friedpies/phaedr-midi-controller/.planning/phases/01-mcu-protocol-foundation/01-04-PLAN.md

---
phase: 01-mcu-protocol-foundation
plan: "04"
type: execute
wave: 1
depends_on: []
files_modified:
  - src/mcuProtocol.h
  - src/mcuProtocol.cpp
autonomous: true
requirements:
  - MCU-01
  - MCU-02

must_haves:
  truths:
    - "Device sends correct Host Connection Query (Step 2) when Logic Pro's Device Query arrives"
    - "Challenge-response validation correctly computes expected bytes from the 4 challenge bytes"
    - "Device sends Confirmation (Step 4) when Logic's reply matches the expected response"
    - "If Logic does not respond, device retries unsolicited Host Connection Query every 5 seconds"
    - "Handshake complete flag is set and accessible after Step 4 confirmation"
  artifacts:
    - path: "src/mcuProtocol.h"
      provides: "MCUProtocol class — SysEx handshake state machine"
      contains: "class MCUProtocol"
    - path: "src/mcuProtocol.cpp"
      provides: "Handshake implementation with challenge-response algorithm"
      contains: "validateChallengeResponse"
  key_links:
    - from: "src/mcuProtocol.cpp"
      to: "usbMIDI.sendSysEx"
      via: "Host Connection Query and Confirmation messages"
      pattern: "sendSysEx"
    - from: "src/mcuProtocol.cpp"
      to: "challenge-response"
      via: "validateChallengeResponse computing expected[0..3]"
      pattern: "expected\\[0\\].*0x7F"
---

<objective>
Create the MCUProtocol class that handles the 4-step Mackie Control Universal SysEx handshake with Logic Pro. This is what causes Logic to recognize the controller as a Mackie Control surface and begin sending bidirectional MIDI feedback.

Purpose: Without a successful handshake, Logic Pro sends no LED feedback and does not route button/fader input to the correct tracks. This is the single gating dependency for the entire phase.
Output: src/mcuProtocol.h and src/mcuProtocol.cpp
</objective>

<execution_context>
@/Users/kenmarut/.claude/get-shit-done/workflows/execute-plan.md
@/Users/kenmarut/.claude/get-shit-done/templates/summary.md
</execution_context>

<context>
@.planning/PROJECT.md
@.planning/ROADMAP.md
@src/pinDefines.h
</context>

<tasks>

<task type="auto">
  <name>Task 1: Create MCUProtocol class — SysEx handshake state machine</name>
  <files>src/mcuProtocol.h, src/mcuProtocol.cpp</files>
  <action>
Create `src/mcuProtocol.h` and `src/mcuProtocol.cpp` implementing the 4-step MCU SysEx handshake.

**Handshake flow (Logic sends first):**
```
Step 1: Logic → Device:  F0 00 00 66 14 00 F7  (Device Query)
Step 2: Device → Logic:  F0 00 00 66 14 01 [serial 7 bytes] [challenge 4 bytes] F7
Step 3: Logic → Device:  F0 00 00 66 14 02 [serial 7 bytes] [response 4 bytes] F7
Step 4: Device → Logic:  F0 00 00 66 14 03 [serial 7 bytes] F7
```

Device name: "Phaedr" — serial bytes are `0x50 0x48 0x41 0x45 0x44 0x52 0x00` (ASCII "PHAEDR\0")
Per CONTEXT.md locked decision: "Device name: Phaedr — this is what Logic Pro displays."

**src/mcuProtocol.h:**
```cpp
#ifndef mcu_protocol_h
#define mcu_protocol_h

#include <Arduino.h>

class MCUProtocol
{
public:
    MCUProtocol();

    // Call from setup() to register SysEx callback and start retry timer
    void begin();

    // Call from loop() to handle retry timer (sends unsolicited query if no response in 5s)
    void update();

    // SysEx callback — register with usbMIDI.setHandleSystemExclusive()
    // Must be called from main.cpp's static SysEx handler which forwards to this
    void handleSysEx(const uint8_t* data, uint16_t length, bool complete);

    bool isHandshakeComplete() const { return _handshakeComplete; }

private:
    void sendHostConnectionQuery();
    void sendConfirmation();
    bool validateChallengeResponse(const uint8_t response[4]) const;

    bool _handshakeComplete;
    unsigned long _lastRetryMs;
    static const unsigned long RETRY_INTERVAL_MS = 5000;  // retry every 5 seconds

    // Device identity — "PHAEDR\0" per CONTEXT.md locked decision
    static const uint8_t MCU_HEADER[5];   // F0 00 00 66 14
    static const uint8_t SERIAL[7];        // 0x50 0x48 0x41 0x45 0x44 0x52 0x00

    // Static challenge bytes — fixed for simplicity; could be randomized later
    // 4 non-zero 7-bit bytes
    static const uint8_t CHALLENGE[4];    // 0x7A 0x6B 0x5C 0x4D
};

extern MCUProtocol mcuProtocol;

#endif
```

**src/mcuProtocol.cpp:**
```cpp
#include "mcuProtocol.h"

// MCU SysEx header: F0 00 00 66 14 (Mackie Control Universal, model 0x14)
const uint8_t MCUProtocol::MCU_HEADER[5] = {0xF0, 0x00, 0x00, 0x66, 0x14};

// "PHAEDR\0" in ASCII — per CONTEXT.md locked decision
const uint8_t MCUProtocol::SERIAL[7] = {0x50, 0x48, 0x41, 0x45, 0x44, 0x52, 0x00};

// Static challenge bytes — 4 non-zero 7-bit values
const uint8_t MCUProtocol::CHALLENGE[4] = {0x7A, 0x6B, 0x5C, 0x4D};

MCUProtocol mcuProtocol;

MCUProtocol::MCUProtocol()
    : _handshakeComplete(false), _lastRetryMs(0)
{
}

void MCUProtocol::begin()
{
    // Send an unsolicited Host Connection Query on startup.
    // If Logic is already running with this surface configured, it responds with a reply.
    // If Logic hasn't started yet, the retry timer in update() resends every 5 seconds.
    sendHostConnectionQuery();
    _lastRetryMs = millis();
}

void MCUProtocol::update()
{
    if (_handshakeComplete) return;

    // Retry unsolicited query if Logic hasn't responded
    if (millis() - _lastRetryMs >= RETRY_INTERVAL_MS) {
        sendHostConnectionQuery();
        _lastRetryMs = millis();
    }
}

void MCUProtocol::handleSysEx(const uint8_t* data, uint16_t length, bool complete)
{
    // Only process complete messages
    if (!complete) return;

    // Minimum length: 7 bytes (header 5 + msgType 1 + F7 1)
    if (length < 7) return;

    // Verify MCU header: F0 00 00 66 14
    if (memcmp(data, MCU_HEADER, 5) != 0) return;

    uint8_t msgType = data[5];

    if (msgType == 0x00) {
        // Step 1: Device Query received from Logic
        // Respond with Host Connection Query (Step 2)
        sendHostConnectionQuery();
        _lastRetryMs = millis();  // reset retry timer

    } else if (msgType == 0x02) {
        // Step 3: Host Connection Reply from Logic
        // Message layout: F0 00 00 66 14 02 [serial 7] [response 4] F7
        // response bytes start at data[13]
        if (length < 18) return;  // too short to contain serial + response

        const uint8_t* response = data + 13;
        if (validateChallengeResponse(response)) {
            sendConfirmation();
            _handshakeComplete = true;
        }
        // If validation fails, do not confirm. Logic will retry the Device Query.
    }
}

void MCUProtocol::sendHostConnectionQuery()
{
    // Step 2: Host Connection Query
    // Format: F0 00 00 66 14 01 [serial 7 bytes] [challenge 4 bytes] F7
    // Total: 18 bytes
    uint8_t msg[18];
    msg[0] = 0xF0;
    msg[1] = 0x00;
    msg[2] = 0x00;
    msg[3] = 0x66;
    msg[4] = 0x14;
    msg[5] = 0x01;                          // message type: Host Connection Query
    memcpy(msg + 6, SERIAL, 7);             // device serial "PHAEDR\0"
    memcpy(msg + 13, CHALLENGE, 4);         // challenge bytes
    msg[17] = 0xF7;
    usbMIDI.sendSysEx(18, msg, true);       // hasTerm=true: msg already has F0 and F7
}

void MCUProtocol::sendConfirmation()
{
    // Step 4: Host Connection Confirmation
    // Format: F0 00 00 66 14 03 [serial 7 bytes] F7
    // Total: 14 bytes
    uint8_t confirm[14];
    confirm[0] = 0xF0;
    confirm[1] = 0x00;
    confirm[2] = 0x00;
    confirm[3] = 0x66;
    confirm[4] = 0x14;
    confirm[5] = 0x03;                       // message type: Host Connection Confirmation
    memcpy(confirm + 6, SERIAL, 7);          // device serial "PHAEDR\0"
    confirm[13] = 0xF7;
    usbMIDI.sendSysEx(14, confirm, true);    // hasTerm=true
}

bool MCUProtocol::validateChallengeResponse(const uint8_t response[4]) const
{
    // Challenge-response algorithm from Ardour source.cc (open source, verified):
    // https://github.com/ardour/ardour/blob/master/libs/surfaces/mackie/surface.cc
    // c = CHALLENGE (4 bytes sent by device in Step 2)
    // r = response (4 bytes received from Logic in Step 3)
    const uint8_t* c = CHALLENGE;
    uint8_t expected[4];
    expected[0] = 0x7F & (c[0] + (c[1] ^ 0x0A) - c[3]);
    expected[1] = 0x7F & ((c[2] >> 4) ^ (c[0] + c[3]));
    expected[2] = 0x7F & ((c[3] - (c[2] << 2)) ^ (c[0] | c[1]));
    expected[3] = 0x7F & (c[1] - c[2] + (0xF0 ^ (c[3] << 4)));
    return memcmp(expected, response, 4) == 0;
}
```

**Important notes for executor:**
- `usbMIDI.sendSysEx(length, data, hasTerm)`: when `hasTerm=true`, the data array already includes F0 (first byte) and F7 (last byte). The library does NOT add them again. Double-check all sendSysEx calls have the correct length and the array actually starts with F0 and ends with F7.
- The `extern MCUProtocol mcuProtocol` declaration in the header allows main.cpp to call `mcuProtocol.begin()` and `mcuProtocol.update()` and to forward the SysEx callback.
- Logic Pro requires the surface to be manually configured in Preferences → Control Surfaces → Setup → New → Mackie Control before it sends any SysEx. This is a user setup step, not a firmware bug.
  </action>
  <verify>Files exist: `ls /Users/kenmarut/repo/phaedr-midi-controller/src/mcuProtocol.*`. Confirm: `grep "PHAEDR" /Users/kenmarut/repo/phaedr-midi-controller/src/mcuProtocol.cpp` shows the serial bytes. `grep "validateChallengeResponse" /Users/kenmarut/repo/phaedr-midi-controller/src/mcuProtocol.cpp` shows the function. `grep "sendSysEx" /Users/kenmarut/repo/phaedr-midi-controller/src/mcuProtocol.cpp` shows calls with hasTerm=true. Run `pio run` — build must succeed.</verify>
  <done>src/mcuProtocol.h and src/mcuProtocol.cpp exist. MCUProtocol handles Step 1 (Device Query) by sending Step 2 (Host Connection Query). MCUProtocol validates Step 3 (Host Connection Reply) using the Ardour challenge-response algorithm and sends Step 4 (Confirmation). Device serial is "PHAEDR\0" per CONTEXT.md locked decision. Retry timer sends unsolicited query every 5 seconds until handshake completes.</done>
</task>

</tasks>

<verification>
From repo root:
1. `pio run` — build must succeed
2. `grep "0x50, 0x48, 0x41, 0x45, 0x44, 0x52" /Users/kenmarut/repo/phaedr-midi-controller/src/mcuProtocol.cpp` — must show SERIAL array with "PHAEDR\0" bytes
3. `grep "hasTerm=true\|true)" /Users/kenmarut/repo/phaedr-midi-controller/src/mcuProtocol.cpp` — sendSysEx calls must use hasTerm=true
4. `grep "expected\[0\]" /Users/kenmarut/repo/phaedr-midi-controller/src/mcuProtocol.cpp` — challenge-response computation must be present
5. `grep "_handshakeComplete = true" /Users/kenmarut/repo/phaedr-midi-controller/src/mcuProtocol.cpp` — set after successful validation
</verification>

<success_criteria>
- src/mcuProtocol.h and src/mcuProtocol.cpp exist and compile without errors
- MCUProtocol::handleSysEx processes message type 0x00 (Device Query) and sends Step 2 response
- MCUProtocol::handleSysEx processes message type 0x02 (Host Connection Reply) with challenge-response validation
- Confirmation (Step 4) sent only when validation passes
- Retry timer: unsolicited Step 2 query sent every 5 seconds until handshake completes
- Device serial "PHAEDR\0" correctly encoded as 0x50 0x48 0x41 0x45 0x44 0x52 0x00
</success_criteria>

<output>
After completion, create `.planning/phases/01-mcu-protocol-foundation/01-04-SUMMARY.md`
</output>
