friedpies/phaedr-midi-controller/.planning/phases/01-mcu-protocol-foundation/01-05-PLAN.md

---
phase: 01-mcu-protocol-foundation
plan: "05"
type: execute
wave: 2
depends_on:
  - "01-01"
  - "01-02"
  - "01-03"
  - "01-04"
files_modified:
  - src/inputManager.h
  - src/inputManager.cpp
  - src/main.cpp
autonomous: false
requirements:
  - MCU-01
  - MCU-02
  - MCU-03
  - MCU-04
  - MCU-05
  - MCU-06
  - LED-01
  - LED-02
  - LED-04
  - BOOT-01
  - PWR-01

must_haves:
  truths:
    - "Plugging in the Teensy triggers a visible cascade LED animation across all 24 LEDs before any MIDI activity"
    - "Logic Pro shows 'Mackie Control' as an active surface after Teensy powers on"
    - "Pressing a channel strip button (REC/SOLO/MUTE/SELECT) causes Logic to send Note On back and the hardware LED lights up"
    - "Moving a slider causes Logic's on-screen fader to move; MIDI monitor confirms Pitch Bend (not CC) on fader's MIDI channel"
    - "Pressing Play, Stop, or Record on the hardware triggers the corresponding transport action in Logic"
    - "No 'CONTROL CHANGE' or 'HANDLE CLOCK' Serial output appears in the serial monitor during operation"
  artifacts:
    - path: "src/inputManager.h"
      provides: "InputManager with MCUButton[] for grid/track, Fader[] for sliders, Potentiometer[] for knobs (CC 16-23)"
      contains: "MCUButton"
    - path: "src/inputManager.cpp"
      provides: "InputManager wiring: NoteRegistry registration, handleNoteMessage routing"
      contains: "noteRegistry.registerButton"
    - path: "src/main.cpp"
      provides: "main.cpp with SysEx handler, NoteOn/Off handlers, mcuProtocol wiring"
      contains: "mcuProtocol.begin"
  key_links:
    - from: "src/main.cpp"
      to: "src/mcuProtocol.cpp"
      via: "mcuProtocol.handleSysEx() called from static SysEx callback"
      pattern: "mcuProtocol\\.handleSysEx"
    - from: "src/main.cpp"
      to: "src/noteRegistry.cpp"
      via: "noteRegistry.getButton(note)->setLedState(velocity)"
      pattern: "noteRegistry\\.getButton"
    - from: "src/inputManager.cpp"
      to: "src/mcuButton.cpp"
      via: "NoteRegistry registration with MCUButton* pointers"
      pattern: "noteRegistry\\.registerButton"
    - from: "src/inputManager.h"
      to: "src/fader.h"
      via: "Fader trackFaders[NUM_TRACKS] replacing trackSliders"
      pattern: "Fader trackFaders"
---

<objective>
Wire all four new classes (MCUButton, NoteRegistry, Fader, MCUProtocol) into InputManager and main.cpp. This plan transforms the complete firmware from CC-based to MCU protocol. After this plan, the firmware is fully functional: Logic Pro recognizes the device, channel buttons send Note Bangs, sliders send Pitch Bend, LEDs respond to Logic feedback.

Purpose: The integration plan — everything built in Wave 1 (Plans 01–04) gets connected here.
Output: Rewritten src/inputManager.h, src/inputManager.cpp, and src/main.cpp
</objective>

<execution_context>
@/Users/kenmarut/.claude/get-shit-done/workflows/execute-plan.md
@/Users/kenmarut/.claude/get-shit-done/templates/summary.md
</execution_context>

<context>
@.planning/PROJECT.md
@.planning/ROADMAP.md
@.planning/STATE.md
@src/pinDefines.h
@src/mcuButton.h
@src/noteRegistry.h
@src/fader.h
@src/mcuProtocol.h
@src/potentiometer.h
@.planning/phases/01-mcu-protocol-foundation/01-01-SUMMARY.md
@.planning/phases/01-mcu-protocol-foundation/01-02-SUMMARY.md
@.planning/phases/01-mcu-protocol-foundation/01-03-SUMMARY.md
@.planning/phases/01-mcu-protocol-foundation/01-04-SUMMARY.md
</context>

<tasks>

<task type="auto">
  <name>Task 1: Rewrite InputManager — MCUButton arrays, Fader arrays, NoteRegistry registration</name>
  <files>src/inputManager.h, src/inputManager.cpp</files>
  <action>
Rewrite `src/inputManager.h` and `src/inputManager.cpp` to use the new MCU classes. This is a full replacement of the old CC-based implementation.

**Hardware constraint — MCU-04 scope on this controller:**
MCU-04 requires transport note bangs for Rewind (note 91), FastForward (note 92), Stop (note 93), Play (note 94), and Record (note 95). This hardware controller has NO physical Rewind or FastForward buttons — the 4x4 grid's bottom row is Shift/Record/Stop/Play, and the upper 12 buttons are navigation functions (Phase 3). Rewind and FastForward are absent by hardware design, not an oversight. MCU-04 is satisfied on this hardware by implementing Stop (93), Play (94), and Record (95). Do NOT add phantom button assignments for notes 91 or 92.

**src/inputManager.h — key changes:**
- Replace `Button gridButtons[]` and `Button trackButtons[]` with `MCUButton` arrays
- Replace `Potentiometer trackSliders[]` with `Fader trackFaders[]`
- Keep `Potentiometer trackKnobs[]` but change CC numbers to MCU-06 mapping (CC 16–23)
- Replace `ButtonRegistry buttonRegistry` with `NoteRegistry noteRegistry`
- Add `handleNoteMessage(byte note, uint8_t velocity)` to route incoming Note On/Off to LED

**MCU note number assignments for channel strip buttons:**
The 8 track buttons (P1–P8) map to MCU REC buttons (notes 0–7). This is the Phase 1 foundation — full 32-button channel strip (REC/SOLO/MUTE/SELECT) expansion happens in Phase 3 when grid buttons are mapped. For Phase 1, the 8 track buttons are the primary channel strip.

Track buttons → MCU REC notes 0–7 (Ch1 REC = note 0, Ch8 REC = note 7)

**Grid button note assignments — REQUIRED mapping (MCU-04):**

K14, K15, and K16 are the transport buttons per CONTEXT.md. These MUST be assigned the exact MCU transport note numbers specified by MCU-04. Do NOT use the generic MUTE/SELECT placeholder for these three buttons:

```
K14_SW / LED_K14 → note 95  (Record)   — MCU-04 required
K15_SW / LED_K15 → note 93  (Stop)     — MCU-04 required, no LED feedback (CONTEXT.md: Stop has no LED)
K16_SW / LED_K16 → note 94  (Play)     — MCU-04 required, no LED feedback (CONTEXT.md: Play has no LED)
```

Note: K15 (Stop) and K16 (Play) have no LED hardware per CONTEXT.md. Construct their MCUButton with a sentinel/invalid LED pin value (e.g., -1 or 255) and guard `setLedState()` in MCUButton to do nothing when LED pin is invalid. Do NOT register K15 or K16 in the NoteRegistry — they send Note Bangs but receive no LED feedback from Logic. DO register K14 (Record, note 95) in the NoteRegistry — it has a LED and Logic sends back record-arm state.

Grid buttons K1–K12 (Phase 1 placeholder — Phase 3 assigns final notes):
Map K1–K8 to MUTE notes 16–23 and K9–K12 to SELECT notes 24–27. These are placeholder assignments consistent with MCU channel strip layout; Phase 3 will reassign specific buttons (cursor, bank, loop, metronome, shift) to their correct MCU note numbers.

K13 (Shift) — Claude's discretion: leave unmapped (no NoteRegistry registration, no note send on press) or assign note 84 (MCU Shift) if the MCUButton class supports a "send but no LED" pattern. Prefer leaving it unmapped in Phase 1 since the Shift layer is a Phase 3 feature.

**Full grid button note assignment table for inputManager.cpp init():**
```
K1_SW / LED_K1   → note 16  (MUTE Ch1, placeholder)
K2_SW / LED_K2   → note 17  (MUTE Ch2, placeholder)
K3_SW / LED_K3   → note 18  (MUTE Ch3, placeholder)
K4_SW / LED_K4   → note 19  (MUTE Ch4, placeholder)
K5_SW / LED_K5   → note 20  (MUTE Ch5, placeholder)
K6_SW / LED_K6   → note 21  (MUTE Ch6, placeholder)
K7_SW / LED_K7   → note 22  (MUTE Ch7, placeholder)
K8_SW / LED_K8   → note 23  (MUTE Ch8, placeholder)
K9_SW / LED_K9   → note 24  (SELECT Ch1, placeholder)
K10_SW / LED_K10 → note 25  (SELECT Ch2, placeholder)
K11_SW / LED_K11 → note 26  (SELECT Ch3, placeholder)
K12_SW / LED_K12 → note 27  (SELECT Ch4, placeholder)
K13_SW / LED_K13 → unmapped (Shift — Phase 3)
K14_SW / LED_K14 → note 95  (Record — MCU-04 REQUIRED)
K15_SW / LED_K15 → note 93  (Stop   — MCU-04 REQUIRED, no LED)
K16_SW / LED_K16 → note 94  (Play   — MCU-04 REQUIRED, no LED)
```
Note: Rewind (note 91) and FastForward (note 92) are NOT assigned to any button. This hardware controller has no physical Rewind or FF buttons — MCU-04 is satisfied by the three buttons that do exist on this hardware (Stop, Play, Record).

Register all buttons with LEDs in NoteRegistry EXCEPT K13 (unmapped), K15 (no LED), and K16 (no LED).

**Complete knob CC reassignment (MCU-06):**
```
trackKnobs: CC 16, 17, 18, 19, 20, 21, 22, 23
(was: CC 14, 15, 28, 29, 30, 31, 118, 119)
```

**handleNoteMessage behavior:**
```cpp
void InputManager::handleNoteMessage(byte note, uint8_t velocity) {
    MCUButton* btn = noteRegistry.getButton(note);
    if (btn != nullptr) {
        btn->setLedState(velocity);
        // velocity 0 (from NoteOff or NoteOn+vel0) = LED off
        // velocity 127 = LED on
        // velocity 1 = blink (Phase 2)
    }
}
```

**src/inputManager.h structure:**
```cpp
#include "mcuButton.h"
#include "fader.h"
#include "noteRegistry.h"
#include "potentiometer.h"
// (remove button.h and buttonRegistry.h includes)

class InputManager {
public:
    void init();
    void readAll();
    void handleNoteMessage(byte note, uint8_t velocity);
    // (remove handleControlChangeMessage — CC-based LED routing is gone)

    static const int NUM_GRID_BUTTONS = 16;
    static const int NUM_TRACKS = 8;
    static const int DEBOUNCE_TIME = 20;

    NoteRegistry noteRegistry;

    MCUButton gridButtons[NUM_GRID_BUTTONS];   // initialized in .cpp or inline
    MCUButton trackButtons[NUM_TRACKS];         // track channel strip (notes 0-7 for REC)
    Fader trackFaders[NUM_TRACKS];              // pitch bend on channels 1-8
    Potentiometer trackKnobs[NUM_TRACKS];       // CC 16-23 (MCU-06)
};
```

**Note on array initialization:** MCUButton and Fader need constructor arguments. Since C++ doesn't allow in-class initializer lists for arrays of non-trivially-constructible types without default constructors, either:
1. Add default constructors to MCUButton and Fader, and initialize in `init()`
2. Use a static factory pattern
3. Use aggregate initialization with explicit constructors

Preferred approach (Claude's discretion): Add a default constructor `MCUButton()` and `Fader()` that initializes to invalid/sentinel values, then call a `setup(pin, ledPin, noteNum, debounceTime)` method in `init()`. This is the cleanest pattern for Arduino where `new` is discouraged.

Alternatively, keep array construction inline in the header using the full constructor, matching the existing codebase pattern. Look at how the existing `inputManager.h` initializes `Potentiometer trackKnobs[]` inline — replicate that pattern for MCUButton and Fader.

Consult `src/pinDefines.h` for the correct pin names for all 16 grid buttons, 8 track buttons, and 8 sliders.

**In inputManager.cpp init():** Call `noteRegistry.registerButton(noteNum, &mcuButton)` for every button that should receive LED feedback. Track buttons (P1–P8) map to notes 0–7. Grid buttons register per the table above (excluding K13, K15, K16).
  </action>
  <verify>Run `pio run` from repo root. Build must succeed. Confirm: `grep "MCUButton" /Users/kenmarut/repo/phaedr-midi-controller/src/inputManager.h` returns result. `grep "Fader trackFaders" /Users/kenmarut/repo/phaedr-midi-controller/src/inputManager.h` returns result. `grep "CC 16" /Users/kenmarut/repo/phaedr-midi-controller/src/inputManager.h` or `.cpp` confirms knob CC update. `grep "95" /Users/kenmarut/repo/phaedr-midi-controller/src/inputManager.cpp` confirms Record note 95 assignment. `grep "93\|94" /Users/kenmarut/repo/phaedr-midi-controller/src/inputManager.cpp` confirms Stop (93) and Play (94) note assignments.</verify>
  <done>inputManager.h uses MCUButton[], Fader[], NoteRegistry. inputManager.cpp init() assigns K14→note 95 (Record), K15→note 93 (Stop), K16→note 94 (Play) explicitly per MCU-04. K1–K12 use MUTE/SELECT placeholder notes. All LED-equipped buttons registered in NoteRegistry (K15 and K16 excluded — no LED hardware). handleNoteMessage() routes incoming note+velocity to correct MCUButton::setLedState(). Knobs use CC 16–23. Build succeeds. No assignments exist for notes 91 or 92 — this hardware has no Rewind or FF buttons.</done>
</task>

<task type="auto">
  <name>Task 2: Rewrite main.cpp — MCU SysEx, NoteOn/Off handlers, remove CC handler</name>
  <files>src/main.cpp</files>
  <action>
Rewrite `src/main.cpp` to use MCUProtocol for SysEx handling, route NoteOn/Off to InputManager for LED feedback, and remove the legacy CC handler. This is a complete replacement of the old main.cpp.

**New main.cpp structure:**

```cpp
#include <Arduino.h>
#include <SoftPWM.h>
#include "pinDefines.h"
#include "inputManager.h"
#include "mcuProtocol.h"

InputManager inputManager;

// BOOT-01: Cascade startup animation — lights all 24 LEDs in sequence then turns them off.
// Runs blocking in setup() BEFORE usbMIDI handlers are registered. Safe because no MIDI
// callbacks are active yet. Confirms all LED hardware works on every power-on.
// LED order: K1–K16 (grid, row by row), then P1–P8 (track buttons).
static void playStartupAnimation()
{
    const int gridLeds[]  = { LED_K1, LED_K2, LED_K3, LED_K4, LED_K5, LED_K6, LED_K7, LED_K8,
                               LED_K9, LED_K10, LED_K11, LED_K12, LED_K13, LED_K14, LED_K15, LED_K16 };
    const int trackLeds[] = { LED_P1, LED_P2, LED_P3, LED_P4, LED_P5, LED_P6, LED_P7, LED_P8 };

    // Light each grid LED in sequence
    for (int i = 0; i < 16; i++) {
        SoftPWMSet(gridLeds[i], LED_MAX_BRIGHTNESS);
        delay(40);
    }
    // Then each track LED
    for (int i = 0; i < 8; i++) {
        SoftPWMSet(trackLeds[i], LED_MAX_BRIGHTNESS);
        delay(40);
    }
    // Hold briefly so user sees all LEDs
    delay(150);
    // Fade all off
    for (int i = 0; i < 16; i++) SoftPWMSet(gridLeds[i], 0);
    for (int i = 0; i < 8; i++)  SoftPWMSet(trackLeds[i], 0);
    delay(300);  // allow SoftPWM fade to complete
}
// Total animation duration: 24 × 40ms + 150 + 300 = ~1.4 seconds

// SysEx handler — forwards to MCUProtocol state machine
void handleSysEx(const uint8_t* data, uint16_t length, bool complete)
{
    mcuProtocol.handleSysEx(data, length, complete);
}

// NoteOn from Logic — LED state feedback
// velocity 127 = LED on, 1 = blink (Phase 2), 0 = LED off
void handleNoteOn(byte channel, byte note, byte velocity)
{
    inputManager.handleNoteMessage(note, velocity);
}

// NoteOff from Logic — LED off
// Some Logic versions send NoteOff instead of NoteOn(vel=0) for LED-off state
void handleNoteOff(byte channel, byte note, byte velocity)
{
    inputManager.handleNoteMessage(note, 0);  // treat NoteOff as velocity 0
}

void setup()
{
    SoftPWMBegin();             // initialize SoftPWM before any SoftPWMSet calls
    playStartupAnimation();     // BOOT-01: cascade animation confirms LEDs work on power-on
    inputManager.init();
    mcuProtocol.begin();

    usbMIDI.setHandleSystemExclusive(handleSysEx);
    usbMIDI.setHandleNoteOn(handleNoteOn);
    usbMIDI.setHandleNoteOff(handleNoteOff);
    // Note: CC handler intentionally removed — per CONTEXT.md clean break decision
    // Note: handleStart/handleClock/handleStop will be added in Phase 4 for beat chaser
}

void loop()
{
    inputManager.readAll();
    mcuProtocol.update();  // handles handshake retry timer
    usbMIDI.read();
}
```

**Key changes from old main.cpp:**
- Remove `#include <MIDIUSB.h>`, `#include <MIDI.h>`, `#include <MIDI.hpp>` (these were incorrect includes for Teensyduino; `usbMIDI` is provided by Teensyduino core directly)
- Remove `#define ENABLEMIDI 1` and its `#ifdef` guard — Teensyduino USB MIDI is always present when the build flag `-DUSB_MIDI_SERIAL` is set
- Remove `handleControlChangeMessage` callback — CC routing is gone (clean break per CONTEXT.md)
- Remove `handleStart`, `handleStop`, `handleClock` stubs — Phase 4 adds these back for beat chaser
- Add `SoftPWMBegin()` in setup() — moved from inputManager.init() since SoftPWM must be initialized before SoftPWMSet calls; or keep it in inputManager.init() if that already handles it (check existing code)
- Register SysEx callback using 3-argument form (`const uint8_t*, uint16_t, bool`) — per RESEARCH.md pitfall 4

**Note on SoftPWMBegin location:** The existing `inputManager.cpp` calls `SoftPWMBegin()` at the start of `init()`. If the new InputManager::init() still calls `SoftPWMBegin()`, do NOT add it again in main.cpp setup(). Avoid double initialization. Check the new inputManager.cpp from Task 1 — if `SoftPWMBegin()` is there, remove it from main.cpp.

**Note on MIDI.h includes:** The existing main.cpp had incorrect `#include <MIDIUSB.h>` and `#include <MIDI.h>` includes. For Teensyduino, `usbMIDI` is a global object provided by the Teensy core when USB MIDI is enabled — no explicit include is needed. Removing these incorrect includes may actually fix a latent compilation issue.

Per CONTEXT.md: "No multi-protocol support, no compile-time mode switch" — no `#ifdef ENABLEMIDI` guard.
  </action>
  <verify>
1. `pio run` — build must succeed with zero errors
2. `grep "handleControlChange" /Users/kenmarut/repo/phaedr-midi-controller/src/main.cpp` — must return NO results (CC handler removed)
3. `grep "mcuProtocol" /Users/kenmarut/repo/phaedr-midi-controller/src/main.cpp` — must show both `mcuProtocol.begin()` and `mcuProtocol.update()`
4. `grep "setHandleSystemExclusive\|setHandleNoteOn\|setHandleNoteOff" /Users/kenmarut/repo/phaedr-midi-controller/src/main.cpp` — all three must be registered
5. `grep "Serial.println" /Users/kenmarut/repo/phaedr-midi-controller/src/main.cpp` — must return no results in callback bodies
6. `grep "playStartupAnimation" /Users/kenmarut/repo/phaedr-midi-controller/src/main.cpp` — must show both the function definition and the call in setup()
  </verify>
  <done>main.cpp registers SysEx, NoteOn, NoteOff handlers. Loop calls inputManager.readAll(), mcuProtocol.update(), usbMIDI.read(). No CC handler present. playStartupAnimation() is defined and called in setup() before MIDI registration. Build succeeds with zero errors.</done>
</task>

<task type="checkpoint:human-verify" gate="blocking">
  <name>Task 3: Hardware verification — Logic Pro surface recognition and LED feedback</name>
  <action>Upload firmware to Teensy 3.5: run `pio run --target upload` from the repo root. This uploads the complete MCU protocol firmware built in Tasks 1 and 2. Wait for upload to complete successfully before presenting the verification steps.</action>
  <verify>`pio run --target upload` exits 0 and reports successful upload to the Teensy 3.5 device.</verify>
  <done>Firmware uploaded successfully. Hardware is ready for interactive verification.</done>
  <what-built>
  Complete MCU protocol firmware: bug fixes (FIX-01, FIX-02), MCUButton class, NoteRegistry, Fader class, MCUProtocol SysEx handshake, and full integration into InputManager and main.cpp. The Teensy 3.5 now speaks MCU protocol instead of custom CC.
  </what-built>
  <how-to-verify>
  Hardware verification required. Perform these steps in order:

  1. Plug in the Teensy (or power-cycle it). Observe the LEDs: all 24 LEDs should light up in cascade sequence — K1 through K16 one at a time (left to right, row by row), then P1 through P8, each held for ~40ms. After the sequence, all LEDs fade off. Total duration ~1.4 seconds. This confirms BOOT-01 and that all LED hardware is functional. If any LED fails to light, note which one (check pinDefines.h pin assignment and wiring).

  2. Open a MIDI monitor (e.g., MIDI Monitor on macOS, or Pocket MIDI). With the Teensy plugged in, press any channel strip track button (P1–P8). The MIDI monitor should show:
     - Note On (channel 1, note 0–7, velocity 127)
     - Note Off (channel 1, note 0–7, velocity 0)
     - NO Control Change messages

  2. Press the three transport buttons on the grid. The MIDI monitor should show:
     - K14 (Record): Note On channel 1, note 95, velocity 127 — then Note Off
     - K15 (Stop):   Note On channel 1, note 93, velocity 127 — then Note Off
     - K16 (Play):   Note On channel 1, note 94, velocity 127 — then Note Off
     - NO Control Change messages
     Note: This hardware has no Rewind or FastForward buttons. Only Stop (93), Play (94), and Record (95) are expected. Notes 91 and 92 will never appear.

  3. Move any slider. The MIDI monitor should show:
     - Pitch Bend on channel 1 (fader 1) through channel 8 (fader 8)
     - NOT Control Change

  4. Configure Logic Pro: Logic Pro → Settings → Control Surfaces → Setup → click "+" → Mackie Control → assign MIDI In/Out to the Teensy USB port. Close the setup panel.

  5. Observe: Logic Pro should show "Mackie Control" as active in the Control Surfaces panel. The Teensy's MIDI connection should show as recognized.

  6. Open a MIDI monitor while Logic is connected. Power-cycle the Teensy (unplug/replug USB). Within 5 seconds, Logic should respond to the SysEx handshake and a confirmation exchange should appear in the MIDI monitor (SysEx messages with header F0 00 00 66 14).

  7. In Logic, press play on a track with a channel strip button configured. The track button's LED on the hardware should light up.

  8. Press Play (K16) on the hardware. Logic should begin playback. Press Stop (K15) — Logic should stop. Press Record (K14) — Logic should toggle record arm; the Record LED on the hardware should reflect Logic's state.

  Expected outcomes:
  - MIDI monitor shows Note Bang (NoteOn+NoteOff) for button presses — not CC
  - Transport buttons send note 94 (Play/K16), 93 (Stop/K15), 95 (Record/K14) — verified in MIDI monitor
  - MIDI monitor shows Pitch Bend for slider movement — not CC
  - Logic Pro shows the device as a recognized Mackie Control surface
  - At least one LED responds to Logic Pro's Note On feedback
  - Pressing Play/Stop in Logic via hardware K16/K15 controls transport

  If Logic does not respond to the handshake: use a MIDI monitor to confirm SysEx is being sent from the Teensy every 5 seconds (the retry timer). If no SysEx appears, check mcuProtocol.begin() is called in setup().

  If transport buttons send wrong note numbers: compare with the note registry in inputManager.cpp — K14 must send note 95, K15 must send note 93, K16 must send note 94.

  If buttons send nothing or wrong note numbers for channel strip: compare with the note registry in inputManager.cpp and the MCU note map in RESEARCH.md.
  </how-to-verify>
  <resume-signal>Type "approved" if hardware verification passes. Describe any issues observed (startup animation missing or LEDs not lighting, wrong note numbers, no LED response, Logic not recognizing the surface, transport buttons not controlling Logic, etc.).</resume-signal>
</task>

</tasks>

<verification>
Build verification (before hardware test):
1. `pio run` — exits 0 with zero errors
2. `grep "MCUButton" /Users/kenmarut/repo/phaedr-midi-controller/src/inputManager.h` — present
3. `grep "Fader trackFaders" /Users/kenmarut/repo/phaedr-midi-controller/src/inputManager.h` — present
4. `grep "noteRegistry.registerButton" /Users/kenmarut/repo/phaedr-midi-controller/src/inputManager.cpp` — present (multiple calls)
5. `grep "95" /Users/kenmarut/repo/phaedr-midi-controller/src/inputManager.cpp` — Record note 95 present (K14)
6. `grep "93\|94" /Users/kenmarut/repo/phaedr-midi-controller/src/inputManager.cpp` — Stop (93) and Play (94) present (K15, K16)
7. `grep "mcuProtocol.begin" /Users/kenmarut/repo/phaedr-midi-controller/src/main.cpp` — present
8. `grep "setHandleSystemExclusive" /Users/kenmarut/repo/phaedr-midi-controller/src/main.cpp` — present

Hardware verification (checkpoint):
- MIDI monitor shows Note Bang on button press (not CC)
- Transport buttons send note 95 (Record/K14), 93 (Stop/K15), 94 (Play/K16) — no Rewind or FF buttons exist on this hardware
- MIDI monitor shows Pitch Bend on slider movement (not CC)
- Logic Pro Control Surfaces panel shows Mackie Control as active surface
- Pressing K16 starts Logic playback, K15 stops it, K14 toggles record arm
</verification>

<success_criteria>
- Firmware compiles and uploads successfully (`pio run --target upload`)
- Plugging in the Teensy triggers a cascade animation: K1→K16 then P1→P8 light up sequentially, then all fade off — visible before any MIDI activity (BOOT-01)
- Button presses produce Note On + Note Off (Note Bang) on MIDI channel 1, not CC
- K14 (Record) sends note 95, K15 (Stop) sends note 93, K16 (Play) sends note 94 — per MCU-04 (hardware scope: Stop/Play/Record only; no Rewind or FF buttons on this controller)
- Slider movement produces Pitch Bend on MIDI channels 1–8, not CC
- Logic Pro recognizes the device as a Mackie Control surface (visible in Control Surfaces setup)
- Channel button LEDs respond to Note On/Off feedback from Logic
- Transport buttons control Logic playback (Play, Stop, Record)
- No Serial debug output in any MIDI callback
- Checkpoint approved by user after hardware verification
</success_criteria>

<output>
After completion, create `.planning/phases/01-mcu-protocol-foundation/01-05-SUMMARY.md`
</output>
