friedpies/phaedr-midi-controller/.planning/phases/01-mcu-protocol-foundation/01-05-SUMMARY.md

---
phase: 01-mcu-protocol-foundation
plan: "05"
subsystem: firmware
tags: [mcu-protocol, teensy, usb-midi, inputmanager, softpwm, pitchbend, note-registry, fader, startup-animation, led-fix]

# Dependency graph
requires:
  - phase: 01-01
    provides: "Bug fixes (FIX-01, FIX-02), Button/ButtonRegistry CC-based system cleaned up"
  - phase: 01-02
    provides: "MCUButton class with Note Bang semantics and NoteRegistry"
  - phase: 01-03
    provides: "Fader class with 14-bit Pitch Bend on MIDI channels 1-8"
  - phase: 01-04
    provides: "MCUProtocol SysEx handshake state machine"
provides:
  - "InputManager rewritten: MCUButton[] for grid/track buttons, Fader[] for sliders, Potentiometer[] with CC 16-23 for knobs"
  - "handleNoteMessage() routes DAW NoteOn/Off to MCUButton::setLedState() via NoteRegistry"
  - "main.cpp: SysEx/NoteOn/NoteOff handlers registered, CC handler removed, playStartupAnimation() BOOT-01 pulse wave animation"
  - "SoftPWM vendored locally with SOFTPWM_MAXCHANNELS=22 to support all 22 LED channels"
  - "Full MCU protocol firmware verified with Logic Pro — surface recognized, LED feedback working, transport buttons control Logic"
affects:
  - "Phase 2 (LED blinking) — MCUButton::setLedState() velocity=1 blink path ready"
  - "Phase 3 (grid button reassignment) — note numbers for K1-K13 are placeholder; Phase 3 reassigns"
  - "Phase 4 (beat chaser) — handleStart/handleClock/handleStop stubs removed; Phase 4 re-adds"

# Tech tracking
tech-stack:
  added:
    - "lib/SoftPWM/ — vendored local copy of SoftPWM 1.0.1 with SOFTPWM_MAXCHANNELS increased from 20 to 22"
  patterns:
    - "Two-phase MCUButton/Fader init: default-construct array, call setup() in init()"
    - "MCUButton sentinel: buttonPin=-1 skips all hardware interaction; noteNum=-1 skips MIDI output"
    - "NoteRegistry: note number to MCUButton* map, registered only for LED-equipped buttons"
    - "BOOT-01 animation: SoftPWMBegin called in inputManager.init(), animation runs after init()"
    - "K13 LED registration: explicit SoftPWMSet(LED_K13, 0) ensures animation works even though MCUButton has ledPin=-1"
    - "Vendor local library override: lib/SoftPWM/ takes precedence over lib_deps in PlatformIO LDF"
    - "Pulse wave animation: 5-LED window sweeps K1->P8 then reverses; SoftPWM fade-out creates comet tail"

key-files:
  created:
    - lib/SoftPWM/SoftPWM.h
    - lib/SoftPWM/SoftPWM.cpp
    - lib/SoftPWM/SoftPWM_timer.h
    - lib/SoftPWM/library.json
  modified:
    - src/inputManager.h
    - src/inputManager.cpp
    - src/main.cpp
    - src/mcuButton.h
    - src/mcuButton.cpp
    - src/fader.h
    - src/fader.cpp
    - platformio.ini

key-decisions:
  - "MCUButton/Fader two-phase init: default constructor + setup() vs inline array init; chose setup() pattern for Arduino where new is discouraged"
  - "K13 (Shift) assigned noteNum=-1: prevents sending note 0 (Ch1 REC) accidentally; read() guards on noteNum < 0"
  - "K15/K16 (Stop/Play) use ledPin=-1 and NOT registered in NoteRegistry — these buttons have no LED hardware per CONTEXT.md"
  - "SoftPWMBegin() remains in inputManager.init(); playStartupAnimation() called after init() so SoftPWM is ready"
  - "MCU-04 hardware scope documented: Rewind (91) and FastForward (92) intentionally absent — no physical buttons on this controller"
  - "SOFTPWM_MAXCHANNELS increased from 20 to 22 via local lib/ vendoring — all 22 LED channels registered successfully"
  - "K13 LED explicitly registered with SoftPWM via SoftPWMSet(LED_K13, 0) despite ledPin=-1 in MCUButton — animation needs the pin registered"
  - "Pulse wave animation chosen over cascade and slosh after user iteration — 5-LED window with comet tail sweeps twice (~4.4s)"

patterns-established:
  - "Sentinel-guarded MCUButton: buttonPin=-1 skips init/read; noteNum=-1 skips MIDI; LED-equipped check via _hasLed"
  - "NoteRegistry selective registration: only register buttons that can receive LED feedback from DAW"
  - "PlatformIO local lib override: place modified library in lib/<name>/ and remove from lib_deps to vendor-pin a dependency"

requirements-completed: [MCU-01, MCU-02, MCU-03, MCU-04, MCU-05, MCU-06, LED-01, LED-02, LED-04, BOOT-01, PWR-01]

# Metrics
duration: ~8min
completed: 2026-02-22
---

# Phase 1 Plan 05: MCU Protocol Integration Summary

**Full MCU firmware integration verified on hardware: InputManager rewritten with MCUButton Note Bangs and 14-bit Fader Pitch Bend, Logic Pro recognizes Mackie Control surface, LED feedback confirmed, pulse wave boot animation across all 24 LEDs — K13 and P8 LED failures diagnosed and fixed (SoftPWM channel limit + unregistered pin)**

## Performance

- **Duration:** ~8 min (execution) + hardware verification iteration
- **Started:** 2026-02-22
- **Completed:** 2026-02-22
- **Tasks:** 3 of 3 (hardware verification approved)
- **Files modified:** 15

## Accomplishments

- Rewrote InputManager: CC-based Button arrays replaced with MCUButton Note Bang arrays; Potentiometer sliders replaced with Fader Pitch Bend arrays; knob CC reassigned to 16-23 (MCU-06)
- Rewrote main.cpp: SysEx/NoteOn/NoteOff handlers registered; CC handler removed; BOOT-01 pulse wave animation runs across all 24 LEDs on power-on; loop calls mcuProtocol.update() for handshake retry
- Added default constructors + setup() to MCUButton and Fader for clean C++ array initialization without heap allocation
- MCU-04 transport buttons correctly assigned: K14=Record(95), K15=Stop(93), K16=Play(94); no phantom Rewind/FF assignments
- Diagnosed K13 LED failure: SoftPWM pin never registered (ledPin=-1 skips MCUButton::init() registration). Fixed with explicit SoftPWMSet(LED_K13, 0) in inputManager.cpp init()
- Diagnosed P8 LED failure: SOFTPWM_MAXCHANNELS=20 exceeded (22 channels required). Fixed by vendoring SoftPWM locally in lib/SoftPWM/ with limit raised to 22
- Hardware verified: Logic Pro shows Mackie Control as active surface; channel strip button LEDs respond to Logic Note On feedback; transport buttons control Logic playback; sliders send Pitch Bend (not CC)
- Iterated startup animation from cascade (one-shot) to slosh (fill/drain) to final pulse wave (5-LED comet sweeps back and forth twice, ~4.4s)

## Task Commits

Each task committed atomically:

1. **Task 1: Rewrite InputManager** - `5c71a55` (feat)
2. **Task 2: Rewrite main.cpp** - `a61ede5` (feat)
3. **Task 3 continuation: LED fix (K13 + P8)** - `3332e1a` (fix)
4. **Animation iteration: slosh startup animation** - `d5a6d30` (feat — superseded)
5. **Animation iteration: final pulse wave animation** - `294b93b` (feat)

**Plan metadata:** `2e31181` (docs: plan 05 completion with LED fixes), `bb36f4b` (earlier docs: plan metadata)

## Files Created/Modified

- `src/inputManager.h` - MCUButton[], Fader[], NoteRegistry, handleNoteMessage(); removed Button[], ButtonRegistry
- `src/inputManager.cpp` - Full init() with setup() calls, NoteRegistry registration, explicit LED_K13 SoftPWM registration, readAll() with faders
- `src/main.cpp` - SysEx/NoteOn/NoteOff handlers, BOOT-01 pulse wave animation, mcuProtocol.begin()/update()
- `src/mcuButton.h` - Added default constructor + setup() declaration
- `src/mcuButton.cpp` - Default constructor, setup(), sentinel guards in init() and read()
- `src/fader.h` - Added default constructor + setup() declaration
- `src/fader.cpp` - Default constructor, setup() implementation
- `platformio.ini` - Removed bhagman/SoftPWM from lib_deps; local lib/ takes precedence
- `lib/SoftPWM/SoftPWM.h` - SOFTPWM_MAXCHANNELS increased from 20 to 22
- `lib/SoftPWM/SoftPWM.cpp` - Vendored copy of SoftPWM 1.0.1 (no logic changes)
- `lib/SoftPWM/SoftPWM_timer.h` - Vendored copy of SoftPWM timer abstractions
- `lib/SoftPWM/library.json` - Local library manifest for PlatformIO LDF

## Decisions Made

- **Two-phase init pattern:** MCUButton and Fader default-construct to sentinel (-1) values then are configured via setup() in InputManager::init(). This avoids heap allocation (no `new`) and matches Arduino embedded idioms.
- **K13 noteNum=-1 sentinel:** K13 (Shift) has valid hardware but no MCU note in Phase 1. Setting noteNum=-1 prevents accidental note 0 output (which is Ch1 REC in MCU protocol). MCUButton::read() guards on `_noteNum < 0`.
- **SoftPWMBegin() location:** Kept in inputManager.init() (not duplicated in main.cpp setup()). playStartupAnimation() called after init() ensures SoftPWM is initialized first.
- **SOFTPWM_MAXCHANNELS=22:** Upstream limit of 20 is insufficient for this controller's 22 LED channels. Vendored locally rather than patching the cache to ensure the fix is durable across PlatformIO updates.
- **Pulse wave animation:** After two iterations (cascade, slosh), the user chose the 5-LED window pulse that sweeps K1 to P8 and back twice (~4.4s). SoftPWM fade-out on the trailing edge creates a comet tail effect.

## Deviations from Plan

### Auto-fixed Issues

**1. [Rule 1 - Bug] MCUButton/Fader missing default constructors for array declaration**
- **Found during:** Task 1 (InputManager rewrite)
- **Issue:** C++ cannot declare `MCUButton gridButtons[16]` without a default constructor — requires all elements to be default-constructible when the array is declared with no initializer
- **Fix:** Added `MCUButton()` and `Fader()` default constructors initializing to sentinel values (-1), plus `setup()` method for two-phase initialization
- **Files modified:** src/mcuButton.h, src/mcuButton.cpp, src/fader.h, src/fader.cpp
- **Committed in:** 5c71a55 (Task 1 commit)

**2. [Rule 1 - Bug] MCUButton::read() would send note 0 for unmapped K13 (Shift)**
- **Found during:** Task 1 (note number assignment review)
- **Issue:** K13 (Shift) has no MCU note in Phase 1; without a guard, pressing K13 would send note 0 (= Ch1 REC in MCU protocol) — wrong behavior
- **Fix:** Set K13 noteNum=-1 and added guard `if (_noteNum < 0) return;` in MCUButton::read() before MIDI output
- **Files modified:** src/mcuButton.cpp, src/inputManager.cpp
- **Committed in:** 5c71a55 (Task 1 commit)

**3. [Rule 1 - Bug] K13 LED (pin 29) not lighting in startup animation**
- **Found during:** Task 3 hardware verification (user reported K13 LED missing)
- **Issue:** K13 has ledPin=-1 in MCUButton so `MCUButton::init()` skips `SoftPWMSet(LED_K13, 0)`. SoftPWM silently ignores `SoftPWMSet()` calls on unregistered pins. The animation tries to light LED_K13 but the pin was never registered.
- **Fix:** Added explicit `SoftPWMSet(LED_K13, 0)` and `SoftPWMSetFadeTime(LED_K13, 125, 125)` in inputManager.cpp init() after the button init loops
- **Files modified:** src/inputManager.cpp
- **Committed in:** 3332e1a (fix)

**4. [Rule 1 - Bug] P8 LED (pin 51) not lighting in startup animation — SoftPWM channel overflow**
- **Found during:** Task 3 hardware verification (user reported P8 LED missing)
- **Issue:** SOFTPWM_MAXCHANNELS=20 is the upstream hard limit. After the K13 fix, 22 channels are needed (K1-K14 grid + P1-P8 track). The 21st and 22nd registrations silently fail — P8 is registered last and is the overflow victim.
- **Root cause count:** K1-K12 (12 LEDs) + K13 (1) + K14 (1) + P1-P8 (8) = 22 channels total
- **Fix:** Vendor SoftPWM locally in `lib/SoftPWM/` with `SOFTPWM_MAXCHANNELS` increased from 20 to 22. Remove `bhagman/SoftPWM` from `lib_deps` since the local copy takes precedence in PlatformIO LDF.
- **Files modified:** lib/SoftPWM/SoftPWM.h, lib/SoftPWM/SoftPWM.cpp, lib/SoftPWM/SoftPWM_timer.h, lib/SoftPWM/library.json, platformio.ini
- **Committed in:** 3332e1a (fix)

### Animation Iteration (user-driven, post-fix)

After all 24 LEDs were verified working, the user iterated on the startup animation style:

- **d5a6d30** — Slosh animation: fill K1→P8 then drain P8→K1, two cycles (~4s). Intermediate version, superseded.
- **294b93b** — Final pulse wave: a 5-LED window sweeps K1→P8 then reverses, twice (~4.4s). SoftPWM fade-out on trailing edge creates a comet tail. This is the shipped version.

These were user-directed style iterations, not bug fixes or plan deviations.

---

**Total deviations:** 4 auto-fixed (all Rule 1 bugs)
**Impact on plan:** All fixes required for correct behavior. No scope creep. Animation iteration was user-directed aesthetic preference.

## Issues Encountered

None beyond the LED failures documented as auto-fixed deviations above.

## User Setup Required

None - no external service configuration required.

## Next Phase Readiness

- Phase 1 fully verified: Logic Pro recognizes the Mackie Control surface; LED feedback, transport buttons, and faders all confirmed working on hardware
- Phase 2 can begin: MCUButton::setLedState() velocity=1 blink path is in place and ready for the pickup mode FSM
- Phase 3 note number grid: K1-K12 use placeholder MUTE/SELECT notes; Phase 3 will reassign cursor, bank, loop, metronome, and shift layer
- Phase 4 animation: playStartupAnimation() is in main.cpp; Phase 4 will add handleStart/handleClock/handleStop for beat chaser

---

## Self-Check: PASSED

- FOUND: src/inputManager.h
- FOUND: src/inputManager.cpp
- FOUND: src/main.cpp
- FOUND: lib/SoftPWM/SoftPWM.h
- FOUND: lib/SoftPWM/library.json
- FOUND: platformio.ini (bhagman/SoftPWM removed from lib_deps)
- FOUND: .planning/phases/01-mcu-protocol-foundation/01-05-SUMMARY.md
- FOUND: commit 5c71a55 (Task 1 — InputManager rewrite)
- FOUND: commit a61ede5 (Task 2 — main.cpp rewrite)
- FOUND: commit 3332e1a (fix — K13 + P8 LED failures)
- FOUND: commit d5a6d30 (feat — slosh animation, superseded)
- FOUND: commit 294b93b (feat — final pulse wave animation)
- Build: SUCCESS (RAM 2.9%, Flash 3.5%) with SoftPWM 1.0.1-local
- Hardware verification: APPROVED by user

---
*Phase: 01-mcu-protocol-foundation*
*Completed: 2026-02-22*
