friedpies/phaedr-midi-controller/.planning/phases/02-led-state-pickup-mode/02-01-PLAN.md

---
phase: 02-led-state-pickup-mode
plan: 01
type: execute
wave: 1
depends_on: []
files_modified:
  - src/mcuButton.h
  - src/mcuButton.cpp
autonomous: true
requirements:
  - PICK-03
  - PICK-04

must_haves:
  truths:
    - "MCUButton has startBlink(periodMs), stopBlink(), updateBlink(), and isBlinking() methods"
    - "updateBlink() drives LED on/off via SoftPWMSet at the given period — half period on, half period off — using millis() delta gating with no delay()"
    - "stopBlink() sets LED dark immediately (no fade confirmation flash)"
    - "setLedState(127) stops any active blink and sets LED solid on; setLedState(0) stops blink and sets LED off — DAW state takes priority"
  artifacts:
    - path: "src/mcuButton.h"
      provides: "MCUButton class declaration with blink API"
      contains: "startBlink"
    - path: "src/mcuButton.cpp"
      provides: "Blink state machine implementation"
      contains: "updateBlink"
  key_links:
    - from: "src/mcuButton.cpp updateBlink()"
      to: "SoftPWMSet(_ledPin, ...)"
      via: "millis()-delta half-period gate"
      pattern: "millis.*_lastBlinkMs.*halfPeriod"
    - from: "src/mcuButton.cpp setLedState()"
      to: "stopBlink()"
      via: "velocity 127 or 0 calls stopBlink() before setting LED"
      pattern: "stopBlink"
---

<objective>
Add a millis()-based LED blink state machine to MCUButton for pickup mode feedback. The blink drives the channel strip button (P1–P8) LED while its corresponding fader is out of sync with the DAW value.

Purpose: PICK-03 requires channel button LED blinking while a fader is out of sync. PICK-04 requires the blink to stop at the exact pickup crossover moment. The blink period is variable — faster when the fader is far from the DAW target, slower as it approaches — giving a "radar ping" feel.

Output: MCUButton with four new public methods (startBlink, stopBlink, updateBlink, isBlinking) and four new private fields. setLedState() updated to stop blinks when DAW sends authoritative LED state.
</objective>

<execution_context>
@/Users/kenmarut/.claude/get-shit-done/workflows/execute-plan.md
@/Users/kenmarut/.claude/get-shit-done/templates/summary.md
</execution_context>

<context>
@.planning/PROJECT.md
@.planning/ROADMAP.md
@.planning/STATE.md
@src/mcuButton.h
@src/mcuButton.cpp
@src/pinDefines.h
</context>

<tasks>

<task type="auto">
  <name>Task 1: Add blink state machine to MCUButton</name>
  <files>src/mcuButton.h
src/mcuButton.cpp</files>
  <action>
Extend MCUButton with a millis()-based blink state machine. Do NOT use delay() — this is an embedded main loop; any blocking call kills MIDI timing.

**src/mcuButton.h additions (in the public section, after existing methods):**

```cpp
void startBlink(uint16_t periodMs);  // activate blink with given period; on/off split is 50/50
void stopBlink();                    // stop blink, set LED dark immediately — no confirmation flash
void updateBlink();                  // call every loop() — no-op if not blinking or no LED
bool isBlinking() const;
```

**src/mcuButton.h additions (in the private section):**

```cpp
bool     _blinking      = false;
uint16_t _blinkPeriodMs = 500;
uint32_t _lastBlinkMs   = 0;
bool     _blinkPhase    = false;  // false = LED off phase, true = LED on phase
```

**src/mcuButton.cpp — implement the four new methods:**

```cpp
void MCUButton::startBlink(uint16_t periodMs) {
    if (!_hasLed) return;
    _blinkPeriodMs = (periodMs < 100) ? 100 : periodMs;  // floor at 100ms
    if (!_blinking) {
        _blinking     = true;
        _blinkPhase   = true;  // start with LED on
        _lastBlinkMs  = millis();
        SoftPWMSet(_ledPin, LED_MAX_BRIGHTNESS);
    }
    // If already blinking, only update period — do not reset phase to avoid flicker
}

void MCUButton::stopBlink() {
    _blinking   = false;
    _blinkPhase = false;
    if (_hasLed) SoftPWMSet(_ledPin, 0);  // go dark immediately — per CONTEXT.md "no confirmation animation"
}

void MCUButton::updateBlink() {
    if (!_blinking || !_hasLed) return;
    uint32_t now        = millis();
    uint32_t halfPeriod = _blinkPeriodMs / 2;
    if (now - _lastBlinkMs >= halfPeriod) {
        _blinkPhase  = !_blinkPhase;
        SoftPWMSet(_ledPin, _blinkPhase ? LED_MAX_BRIGHTNESS : 0);
        _lastBlinkMs = now;
    }
}

bool MCUButton::isBlinking() const { return _blinking; }
```

**src/mcuButton.cpp — update setLedState() to resolve blink/DAW conflict:**

DAW state (velocity 127 = on, 0 = off) must override pickup blink — Logic's LED commands take priority. Update setLedState():

```cpp
void MCUButton::setLedState(uint8_t velocity) {
    if (!_hasLed) return;
    if (velocity == 0) {
        stopBlink();                     // stop blink, LED goes dark
    } else if (velocity == 127) {
        stopBlink();                     // stop blink first
        SoftPWMSet(_ledPin, LED_MAX_BRIGHTNESS);  // then set solid on
    }
    // velocity == 1 from Logic = "blink" command; handled by pickup FSM — ignore here
    // (pickup FSM manages its own startBlink/stopBlink lifecycle)
}
```

The existing `SoftPWMSetFadeTime(_ledPin, 125, 125)` in init() is retained — 125ms fade is fast enough to feel instant for LED-03 mode LEDs per CONTEXT.md. Do not change fade time settings.
  </action>
  <verify>
    <automated>cd /Users/kenmarut/repo/phaedr-midi-controller && pio run 2>&1 | tail -5</automated>
    <manual>Confirm build succeeds with 0 errors and 0 warnings related to mcuButton. The new blink methods will not be called yet (that happens in Plans 02 and 03) — compilation is the only gate here.</manual>
  </verify>
  <done>pio run succeeds with 0 errors. mcuButton.h declares startBlink, stopBlink, updateBlink, isBlinking. mcuButton.cpp implements all four. setLedState() calls stopBlink() on velocity 0 and 127.</done>
</task>

</tasks>

<verification>
Run `pio run` from the project root. Build must succeed with 0 errors. The blink API surface must be in place: startBlink(uint16_t), stopBlink(), updateBlink(), isBlinking() declared in mcuButton.h and defined in mcuButton.cpp.
</verification>

<success_criteria>
1. `pio run` exits 0 — firmware compiles cleanly with new blink methods
2. startBlink(100) enforces a 100ms floor — no sub-100ms periods
3. updateBlink() uses millis()-delta gating — zero delay() calls in the implementation
4. stopBlink() calls SoftPWMSet(_ledPin, 0) — LED goes dark immediately
5. setLedState(127) calls stopBlink() before setting LED solid — no conflict with DAW LED state
6. setLedState(0) calls stopBlink() — blink cannot outlive a DAW LED-off command
</success_criteria>

<output>
After completion, create `.planning/phases/02-led-state-pickup-mode/02-01-SUMMARY.md`
</output>
