friedpies/phaedr-midi-controller/.planning/phases/02-led-state-pickup-mode/02-01-SUMMARY.md

---
phase: 02-led-state-pickup-mode
plan: 01
subsystem: ui
tags: [SoftPWM, millis, blink, MCUButton, LED, pickup-mode]

# Dependency graph
requires:
  - phase: 01-mcu-protocol-foundation
    provides: MCUButton class with setLedState(), SoftPWM init, LED_MAX_BRIGHTNESS constant

provides:
  - MCUButton blink API: startBlink(periodMs), stopBlink(), updateBlink(), isBlinking()
  - millis()-delta half-period blink state machine with 100ms floor
  - DAW-priority LED conflict resolution in setLedState()

affects:
  - 02-02-PLAN (pickup FSM calls startBlink/stopBlink per fader sync state)
  - 02-03-PLAN (updateBlink() must be called in loop via InputManager)

# Tech tracking
tech-stack:
  added: []
  patterns:
    - millis()-delta gating for non-blocking embedded state machines
    - DAW-priority LED conflict resolution: stopBlink() called before any setLedState() that changes LED

key-files:
  created: []
  modified:
    - src/mcuButton.h
    - src/mcuButton.cpp

key-decisions:
  - "startBlink() preserves blinkPhase if already blinking to avoid visual flicker on period updates"
  - "startBlink() floors period at 100ms — sub-100ms blink periods risk visual noise on embedded timer granularity"
  - "stopBlink() is unconditional on setLedState(0/127) — DAW LED state always wins over pickup blink"

patterns-established:
  - "Blink state machine pattern: _blinking flag + _blinkPhase bool + _lastBlinkMs + _blinkPeriodMs private fields, driven by updateBlink() each loop iteration"
  - "DAW-priority LED conflict: call stopBlink() before any SoftPWMSet in setLedState()"

requirements-completed:
  - PICK-03
  - PICK-04

# Metrics
duration: 3min
completed: 2026-02-25
---

# Phase 02 Plan 01: MCUButton Blink State Machine Summary

**millis()-delta LED blink state machine added to MCUButton with 50/50 duty cycle, 100ms period floor, and DAW-priority LED conflict resolution via stopBlink() on setLedState()**

## Performance

- **Duration:** ~3 min
- **Started:** 2026-02-25T23:12:18Z
- **Completed:** 2026-02-25T23:15:30Z
- **Tasks:** 1 of 1
- **Files modified:** 2

## Accomplishments
- Added four public blink methods to MCUButton: `startBlink(uint16_t periodMs)`, `stopBlink()`, `updateBlink()`, `isBlinking() const`
- Implemented millis()-delta half-period gating in `updateBlink()` — zero `delay()` calls, safe for embedded main loop
- `startBlink()` enforces 100ms floor and preserves blink phase on period updates (no flicker when pickup FSM speeds up blink)
- Updated `setLedState()` to call `stopBlink()` on velocity 0 and 127 — DAW LED commands take priority over pickup blink

## Task Commits

Each task was committed atomically:

1. **Task 1: Add blink state machine to MCUButton** - `c431d1f` (feat)

**Plan metadata:** TBD (docs: complete plan)

## Files Created/Modified
- `src/mcuButton.h` - Added 4 public blink methods and 4 private blink state fields
- `src/mcuButton.cpp` - Implemented startBlink, stopBlink, updateBlink, isBlinking; updated setLedState to call stopBlink

## Decisions Made
- `startBlink()` does not reset `_blinkPhase` if already blinking — only updates `_blinkPeriodMs`. This prevents visible flicker when the pickup FSM calls `startBlink()` with an updated period as the fader approaches target.
- `startBlink()` floors at 100ms — sub-100ms periods would create visual noise given SoftPWM's 125ms fade time.
- `stopBlink()` unconditionally goes dark (no confirmation flash) per CONTEXT.md spec.

## Deviations from Plan

None — plan executed exactly as written.

## Issues Encountered

None.

## User Setup Required

None — no external service configuration required.

## Next Phase Readiness
- Blink API surface is complete and compilation-verified
- Plan 02 (pickup FSM) can now call `startBlink(periodMs)` and `stopBlink()` on MCUButton instances
- Plan 03 (InputManager wiring) must add `updateBlink()` call in `readAll()` loop for each track button

---
*Phase: 02-led-state-pickup-mode*
*Completed: 2026-02-25*

## Self-Check: PASSED

- FOUND: src/mcuButton.h
- FOUND: src/mcuButton.cpp
- FOUND: .planning/phases/02-led-state-pickup-mode/02-01-SUMMARY.md
- FOUND commit: c431d1f
