friedpies/phaedr-midi-controller/.planning/phases/02-led-state-pickup-mode/02-02-PLAN.md

---
phase: 02-led-state-pickup-mode
plan: 02
type: execute
wave: 2
depends_on:
  - 02-01
files_modified:
  - src/fader.h
  - src/fader.cpp
autonomous: true
requirements:
  - PICK-01
  - PICK-02
  - PICK-04
  - PICK-05
  - PICK-06

must_haves:
  truths:
    - "Fader stores last known DAW value received via setDawValue(int value14bit)"
    - "Fader MIDI output (sendPitchBend) is suppressed when _pickupState == OUT_OF_SYNC"
    - "First significant physical movement while OUT_OF_SYNC lazily reveals blink on the associated channel button (does NOT blink on bank switch itself)"
    - "Crossover fires when abs(physical14bit - dawValue14bit) <= PICKUP_DEADBAND or both at rail (PICK-06); on crossover, snaps DAW by sending immediate pitch bend"
    - "setDawValue() detects large delta vs prior DAW value and calls enterPickupMode() — simple per-fader bank switch detection"
  artifacts:
    - path: "src/fader.h"
      provides: "Fader class with pickup FSM fields and API"
      contains: "PickupState"
    - path: "src/fader.cpp"
      provides: "Pickup FSM implementation: setDawValue, enterPickupMode, crossover in read()"
      contains: "enterPickupMode"
  key_links:
    - from: "src/fader.cpp setDawValue()"
      to: "enterPickupMode()"
      via: "delta > BANK_SWITCH_THRESHOLD triggers OUT_OF_SYNC"
      pattern: "BANK_SWITCH_THRESHOLD"
    - from: "src/fader.cpp read() OUT_OF_SYNC branch"
      to: "_channelBtn->startBlink()"
      via: "first movement triggers lazy blink reveal"
      pattern: "_blinkRevealed"
    - from: "src/fader.cpp read() crossover check"
      to: "usbMIDI.sendPitchBend"
      via: "snap value sent immediately on pickup"
      pattern: "SYNCED.*sendPitchBend"
---

<objective>
Implement the fader pickup FSM — a two-state machine (SYNCED / OUT_OF_SYNC) per fader that suppresses MIDI output after a bank switch until the physical position enters the deadband around the DAW value.

Purpose: This is the core of Phase 2. Faders that jump to the wrong position after a bank switch silently suppress pitch bend output and blink the channel strip button (via MCUButton from Plan 01) until the user sweeps through the target position. The blink is lazily revealed — only on the user's first physical interaction with that channel, not immediately on bank switch.

Output: Fader class extended with DAW value tracking, pickup FSM, channel button association, and the full crossover detection logic.
</objective>

<execution_context>
@/Users/kenmarut/.claude/get-shit-done/workflows/execute-plan.md
@/Users/kenmarut/.claude/get-shit-done/templates/summary.md
</execution_context>

<context>
@.planning/PROJECT.md
@.planning/ROADMAP.md
@.planning/STATE.md
@src/fader.h
@src/fader.cpp
@src/mcuButton.h
@.planning/phases/02-led-state-pickup-mode/02-01-SUMMARY.md
</context>

<tasks>

<task type="auto">
  <name>Task 1: Add pickup FSM fields and API to Fader</name>
  <files>src/fader.h
src/fader.cpp</files>
  <action>
Extend the Fader class with a two-state pickup FSM (SYNCED / OUT_OF_SYNC), DAW value tracking, and channel button association. All pickup math is done in 14-bit (0–16383) range — never mix with 7-bit MIDI or 10-bit ADC values.

**src/fader.h — replace the full file with the extended version:**

Add at the top (before the class, after #include):
```cpp
#include "mcuButton.h"
```

Add the enum before the class:
```cpp
enum PickupState { SYNCED, OUT_OF_SYNC };
```

Add to the public section (after existing methods):
```cpp
void setDawValue(int value14bit);          // PICK-01: store DAW value, detect bank switch
void enterPickupMode();                    // set OUT_OF_SYNC, reset lazy-reveal flag
void setChannelButton(MCUButton* btn);    // wire to corresponding P1–P8 button

// PICK-02 / PICK-06: pickup deadband and bank switch threshold (all in 14-bit units)
// PICKUP_DEADBAND: ~128 = ≈1 in 7-bit MIDI. Must be > FADER_NOISE_THRESHOLD (48).
// Start at 128; increase if fader noise causes false pickups; decrease if feel is too loose.
static const int PICKUP_DEADBAND        = 128;
// BANK_SWITCH_THRESHOLD: DAW value delta that signals a bank switch vs fader automation.
// 512 in 14-bit ≈ 4 in 7-bit MIDI. Tune up if automation causes false triggers.
static const int BANK_SWITCH_THRESHOLD  = 512;
```

Add to the private section:
```cpp
int         _dawValue14bit  = -1;      // -1 = no DAW value received yet
PickupState _pickupState    = SYNCED;
bool        _blinkRevealed  = false;   // lazy reveal: true after first interaction in OUT_OF_SYNC
MCUButton*  _channelBtn     = nullptr;
```

**src/fader.cpp — implement the three new methods:**

```cpp
void Fader::setChannelButton(MCUButton* btn) {
    _channelBtn = btn;
}

void Fader::enterPickupMode() {
    _pickupState   = OUT_OF_SYNC;
    _blinkRevealed = false;
    // NOTE: do NOT call _channelBtn->startBlink() here — blink is lazily revealed
    // on first user interaction, per CONTEXT.md: "no visual noise by default"
}

void Fader::setDawValue(int newValue14bit) {
    // PICK-05 / bank switch detection: if the DAW value changes by a large amount
    // while this fader is SYNCED, treat it as a bank switch and enter pickup mode.
    // Guard: _dawValue14bit >= 0 ensures we skip the check on first power-on receipt
    // (Pitfall 4 from RESEARCH.md — first bank switch after boot)
    if (_dawValue14bit >= 0 && _pickupState == SYNCED) {
        int delta = abs(newValue14bit - _dawValue14bit);
        if (delta > BANK_SWITCH_THRESHOLD) {
            enterPickupMode();
        }
    }
    _dawValue14bit = newValue14bit;
}
```

**src/fader.cpp — replace Fader::read() with the pickup-FSM-guarded version:**

The existing read() sends pitch bend unconditionally. Replace it entirely:

```cpp
void Fader::read() {
    if (_pin < 0) return;

    int raw        = analogRead(_pin);
    int fader14bit = map(raw, 0, 1023, 0, 16383);

    // Suppress output if change is within noise threshold
    // IMPORTANT: compute significantMove BEFORE early-return so _lastFader14bit is
    // only updated on meaningful changes, keeping the crossover check stable.
    bool significantMove = (_lastFader14bit < 0 ||
                            abs(fader14bit - _lastFader14bit) > FADER_NOISE_THRESHOLD);
    if (!significantMove) return;

    _lastFader14bit = fader14bit;

    if (_pickupState == OUT_OF_SYNC) {
        // --- Lazy blink reveal (CONTEXT.md: no visual noise on bank switch) ---
        // On first significant move while OUT_OF_SYNC: reveal the blink.
        // On subsequent moves: refresh blink period to encode current distance.
        if (_dawValue14bit >= 0 && _channelBtn != nullptr) {
            int distance = abs(fader14bit - _dawValue14bit);
            // Map distance 0..16383 → period 600..200ms (faster = farther from target)
            // Using Arduino map(): linear interpolation between the two extremes.
            uint16_t period = (uint16_t)map(
                min(distance, 16383), 0, 16383, 600, 200);
            _channelBtn->startBlink(period);
            _blinkRevealed = true;
        }

        // --- Crossover detection (PICK-02, PICK-04, PICK-06) ---
        // Boundary edge case (PICK-06): both physical and DAW at rail → immediate pickup
        bool bothAtZero = (fader14bit <= PICKUP_DEADBAND &&
                           _dawValue14bit >= 0 && _dawValue14bit <= PICKUP_DEADBAND);
        bool bothAtMax  = (fader14bit >= (16383 - PICKUP_DEADBAND) &&
                           _dawValue14bit >= (16383 - PICKUP_DEADBAND));
        // Normal crossover: physical enters deadband around DAW value
        bool inDeadband = (_dawValue14bit >= 0 &&
                           abs(fader14bit - _dawValue14bit) <= PICKUP_DEADBAND);

        if (bothAtZero || bothAtMax || inDeadband) {
            _pickupState = SYNCED;
            if (_channelBtn != nullptr) _channelBtn->stopBlink();
            // PICK-04: immediately send snap value so DAW snaps to match physical position
            usbMIDI.sendPitchBend(fader14bit - 8192, _midiChannel);
        }
        // Suppress MIDI while OUT_OF_SYNC — return without sending
        return;
    }

    // SYNCED: normal pitch bend output
    usbMIDI.sendPitchBend(fader14bit - 8192, _midiChannel);
}
```

**Pitfall guard — do NOT apply deadband using 7-bit units.** PICKUP_DEADBAND = 128 is in 14-bit units. This is intentionally larger than FADER_NOISE_THRESHOLD (48) so ADC jitter cannot cause false pickups, but small enough that the user feels a precise snap point.
  </action>
  <verify>
    <automated>cd /Users/kenmarut/repo/phaedr-midi-controller && pio run 2>&1 | tail -5</automated>
    <manual>Confirm build succeeds with 0 errors. Verify fader.h includes mcuButton.h, declares PickupState enum, and has setDawValue/enterPickupMode/setChannelButton in public section. Verify fader.cpp read() has an OUT_OF_SYNC branch that returns without sendPitchBend.</manual>
  </verify>
  <done>pio run succeeds with 0 errors. Fader class compiles with pickup FSM. The OUT_OF_SYNC branch in read() suppresses sendPitchBend and checks crossover. setDawValue() detects large delta and calls enterPickupMode(). startBlink() is called with a distance-mapped period on first move while OUT_OF_SYNC.</done>
</task>

</tasks>

<verification>
Run `pio run`. Build must succeed with 0 errors. Check that:
- fader.h includes mcuButton.h
- PickupState enum and all new public methods are present
- fader.cpp read() contains the OUT_OF_SYNC guard with return before sendPitchBend
- PICKUP_DEADBAND = 128 (not a 7-bit value like 3)
- BANK_SWITCH_THRESHOLD = 512
</verification>

<success_criteria>
1. `pio run` exits 0 — firmware compiles cleanly
2. PICKUP_DEADBAND is defined in 14-bit units (128), larger than FADER_NOISE_THRESHOLD (48)
3. read() OUT_OF_SYNC branch returns before calling sendPitchBend — MIDI is suppressed
4. Crossover check includes both boundary rail checks (PICK-06) and deadband check (PICK-02)
5. On crossover: _pickupState = SYNCED, stopBlink() called, snap pitch bend sent immediately (PICK-04)
6. setDawValue() guards on _dawValue14bit >= 0 before delta check — no false pickup on first boot
7. enterPickupMode() does NOT call startBlink() — lazy reveal preserved
</success_criteria>

<output>
After completion, create `.planning/phases/02-led-state-pickup-mode/02-02-SUMMARY.md`
</output>
