friedpies/phaedr-midi-controller/.planning/phases/02-led-state-pickup-mode/02-03-PLAN.md

---
phase: 02-led-state-pickup-mode
plan: 03
type: execute
wave: 3
depends_on:
  - 02-02
files_modified:
  - src/mcuConfig.h
  - src/inputManager.h
  - src/inputManager.cpp
  - src/main.cpp
autonomous: false
requirements:
  - LED-03
  - PICK-01
  - PICK-02
  - PICK-03
  - PICK-05
  - PICK-06

must_haves:
  truths:
    - "usbMIDI.setHandlePitchBend(handlePitchBend) is registered in setup() — fader DAW values flow into the firmware"
    - "inputManager.updateBlinks() is called from loop() — all 8 channel button blink state machines advance each iteration"
    - "inputManager.setFaderDawValue() routes incoming pitch bend to the correct Fader::setDawValue()"
    - "Each Fader[i] is associated with trackButtons[i] via setChannelButton() in InputManager::init()"
    - "Grid buttons for Loop, Punch, and Metronome are registered in NoteRegistry so Logic Pro LED state feedback drives their LEDs"
    - "Mode button note numbers are defined in src/mcuConfig.h — not hardcoded inline"
  artifacts:
    - path: "src/mcuConfig.h"
      provides: "Compile-time note numbers and grid indices for Loop/Punch/Metronome"
      contains: "MCU_NOTE_LOOP"
    - path: "src/inputManager.h"
      provides: "updateBlinks() and setFaderDawValue() declarations"
      contains: "updateBlinks"
    - path: "src/inputManager.cpp"
      provides: "Fader-to-channel-button wiring, mode button NoteRegistry wiring, updateBlinks() implementation"
      contains: "setChannelButton"
    - path: "src/main.cpp"
      provides: "handlePitchBend callback registered; updateBlinks() called from loop()"
      contains: "setHandlePitchBend"
  key_links:
    - from: "src/main.cpp handlePitchBend()"
      to: "inputManager.setFaderDawValue()"
      via: "channel index = channel - 1, value14bit = value + 8192"
      pattern: "setFaderDawValue"
    - from: "src/inputManager.cpp updateBlinks()"
      to: "trackButtons[i].updateBlink()"
      via: "loop over NUM_TRACKS"
      pattern: "updateBlink"
    - from: "src/inputManager.cpp init()"
      to: "trackFaders[i].setChannelButton(&trackButtons[i])"
      via: "fader[i] ↔ trackButton[i] association"
      pattern: "setChannelButton"
    - from: "src/inputManager.cpp init()"
      to: "noteRegistry.registerButton(MCU_NOTE_LOOP, &gridButtons[MCU_LOOP_GRID_INDEX])"
      via: "LED-03: mode button LED feedback from Logic"
      pattern: "MCU_NOTE_LOOP"
---

<objective>
Wire all Phase 2 components together: register the pitch bend receive callback in main.cpp, add updateBlinks() and setFaderDawValue() to InputManager, associate each Fader with its channel strip button, create the compile-time mcuConfig.h header for mode note numbers, and register Loop/Punch/Metronome grid buttons in the NoteRegistry for LED-03 feedback.

Purpose: Plans 01 and 02 built the MCUButton blink machine and the Fader pickup FSM in isolation. This plan connects them to the rest of the system — incoming pitch bend from Logic feeds DAW values into faders; the blink update call in loop() drives the blink timers; mode button note numbers from mcuConfig.h map Logic's LED state commands to the correct grid button LEDs.

Output: A complete, building, hardware-testable Phase 2 firmware. A human verification checkpoint confirms the MCU note numbers for Loop/Punch/Metronome (which have LOW confidence from community sources) before those NoteRegistry entries are trusted.
</objective>

<execution_context>
@/Users/kenmarut/.claude/get-shit-done/workflows/execute-plan.md
@/Users/kenmarut/.claude/get-shit-done/templates/summary.md
</execution_context>

<context>
@.planning/PROJECT.md
@.planning/ROADMAP.md
@.planning/STATE.md
@src/main.cpp
@src/inputManager.h
@src/inputManager.cpp
@src/fader.h
@src/mcuButton.h
@src/pinDefines.h
@.planning/phases/02-led-state-pickup-mode/02-02-SUMMARY.md
</context>

<tasks>

<task type="auto">
  <name>Task 1: Create mcuConfig.h and wire InputManager + main.cpp</name>
  <files>src/mcuConfig.h
src/inputManager.h
src/inputManager.cpp
src/main.cpp</files>
  <action>
Four changes in one pass — all integration, no new algorithm complexity.

**1. Create src/mcuConfig.h (NEW FILE)**

This is the compile-time config header for mode button note numbers. Per CONTEXT.md locked decision: "Button-to-function mapping lives in a compile-time config header — not EEPROM, not hardcoded in logic."

```cpp
#ifndef mcu_config_h
#define mcu_config_h

// ============================================================
// MCU Mode Button Note Numbers — Logic Pro LED State Feedback
// ============================================================
// Logic Pro sends Note On (velocity 127 = on, 0 = off) for these functions.
// NoteRegistry routes these notes to the grid button LEDs defined below.
//
// IMPORTANT: These values are from community MCU documentation (MEDIUM confidence).
// Verify with a MIDI monitor or temporary Serial.print in handleNoteOn() before
// relying on them. See RESEARCH.md Pitfall 5 for verification procedure.
//
// To verify: open Logic, enable Serial monitor (pio device monitor), toggle
// Loop/Punch/Metronome in Logic, observe which note numbers appear in Serial output
// (add temporary Serial.print(note) in handleNoteOn if needed), then update below.

// MCU note numbers for transport mode state LEDs
// Loop/Cycle button state:
#define MCU_NOTE_LOOP           86
// Punch In (punch start) state:
#define MCU_NOTE_PUNCH_IN       85
// Metronome/Click toggle state:
#define MCU_NOTE_METRONOME      89

// Grid button indices (0-based, K1=index 0 ... K16=index 15)
// These define which physical grid button receives the LED feedback.
// Current Phase 1 placeholder assignments for K1-K12:
//   K1-K8  (indices 0-7):  MUTE Ch1-Ch8 (note 16-23)
//   K9-K12 (indices 8-11): SELECT Ch1-Ch4 (note 24-27)
// Phase 3 will reassign these when the full grid transport layout is implemented.
// For Phase 2, we wire Loop/Punch/Metronome to grid buttons that are not already
// assigned critical transport functions. K9-K11 (indices 8-10) are SELECT placeholders
// and are appropriate hosts for mode LEDs until Phase 3 finalizes grid layout.
//
// Change these indices in Phase 3 when grid button note assignments are confirmed.
#define MCU_LOOP_GRID_INDEX     8   // K9  — Loop/Cycle LED
#define MCU_PUNCH_GRID_INDEX    9   // K10 — Punch In LED
#define MCU_METRO_GRID_INDEX    10  // K11 — Metronome LED

#endif // mcu_config_h
```

**2. src/inputManager.h — add two public method declarations**

In the public section, after `void handleNoteMessage(...)`, add:
```cpp
void updateBlinks();                            // PICK-03: drive all channel button blink timers
void setFaderDawValue(int faderIdx, int val14bit); // PICK-01: route incoming pitch bend to fader
```

**3. src/inputManager.cpp — three additions**

At the top, add include:
```cpp
#include "mcuConfig.h"
```

Inside `InputManager::init()`, after all the `trackFaders[i].setup(...)` calls (after `trackFaders[7].setup(SLIDE_8, 8);`) and before the "Init all buttons" section, add the channel button associations:
```cpp
// PICK-03/PICK-04: Associate each fader with its channel strip button for blink control.
// fader[0] (MIDI ch1, SLIDE_1) ↔ trackButtons[0] (P1), ..., fader[7] ↔ trackButtons[7] (P8)
for (int i = 0; i < NUM_TRACKS; i++) {
    trackFaders[i].setChannelButton(&trackButtons[i]);
}
```

At the end of `InputManager::init()`, after the existing `noteRegistry.registerButton(7, &trackButtons[7])` line, add:
```cpp
// LED-03: Loop/Punch/Metronome grid button LED feedback from Logic Pro.
// Note numbers defined in mcuConfig.h — update there after hardware MIDI monitor verification.
noteRegistry.registerButton(MCU_NOTE_LOOP,      &gridButtons[MCU_LOOP_GRID_INDEX]);
noteRegistry.registerButton(MCU_NOTE_PUNCH_IN,  &gridButtons[MCU_PUNCH_GRID_INDEX]);
noteRegistry.registerButton(MCU_NOTE_METRONOME, &gridButtons[MCU_METRO_GRID_INDEX]);
```

Add two new method implementations (append to end of file):
```cpp
void InputManager::updateBlinks() {
    // PICK-03: advance blink state machines for all 8 channel strip buttons.
    // Must be called every loop() iteration — millis()-delta gating ensures no blocking.
    for (int i = 0; i < NUM_TRACKS; i++) {
        trackButtons[i].updateBlink();
    }
}

void InputManager::setFaderDawValue(int faderIdx, int value14bit) {
    // PICK-01: route incoming pitch bend (from handlePitchBend in main.cpp) to the correct fader.
    // faderIdx is 0-based (caller passes channel - 1).
    if (faderIdx < 0 || faderIdx >= NUM_TRACKS) return;
    trackFaders[faderIdx].setDawValue(value14bit);
}
```

**4. src/main.cpp — two additions**

Add the pitch bend receive callback before setup() (after handleNoteOff):
```cpp
// PICK-01: Receive fader position feedback from Logic Pro.
// Logic sends Pitch Bend on MIDI channels 1-8 to tell the controller each fader's current DAW value.
// Teensyduino callback: value is signed -8192..+8191; convert to 14-bit 0..16383 with +8192 offset.
void handlePitchBend(byte channel, int value) {
    if (channel >= 1 && channel <= 8) {
        inputManager.setFaderDawValue(channel - 1, value + 8192);
    }
}
```

In `setup()`, after `usbMIDI.setHandleNoteOff(handleNoteOff)`, add:
```cpp
usbMIDI.setHandlePitchBend(handlePitchBend);  // PICK-01: receive fader DAW values from Logic
```

In `loop()`, inside the `if (mcuProtocol.isHandshakeComplete())` branch, after `inputManager.readAll()`, add:
```cpp
inputManager.updateBlinks();  // PICK-03: advance channel button blink state machines
```

The final loop() should look like:
```cpp
void loop()
{
    if (mcuProtocol.isHandshakeComplete()) {
        inputManager.readAll();
        inputManager.updateBlinks();  // PICK-03: advance channel button blink state machines
    } else {
        inputManager.readIdle();
        inputManager.updateRipple();
    }
    mcuProtocol.update();
    usbMIDI.read();
}
```

**Critical ordering note:** The setChannelButton() associations MUST be added BEFORE the "Init all buttons" loop in init(). The init() calls do not use the channel button pointer, so order doesn't strictly matter at runtime, but keeping setup data together is cleaner. If the Fader::setup() call changes in future, the pointer wiring stays logically adjacent.
  </action>
  <verify>
    <automated>cd /Users/kenmarut/repo/phaedr-midi-controller && pio run 2>&1 | tail -10</automated>
    <manual>Confirm build succeeds with 0 errors. Verify mcuConfig.h exists in src/. Verify main.cpp has handlePitchBend function and setHandlePitchBend registration. Verify inputManager.cpp has updateBlinks() and setFaderDawValue() implementations.</manual>
  </verify>
  <done>pio run succeeds with 0 errors. All four files modified. mcuConfig.h created. handlePitchBend registered in main.cpp setup(). updateBlinks() called in main.cpp loop(). setChannelButton() associations wired in InputManager::init(). LED-03 NoteRegistry entries present for MCU_NOTE_LOOP, MCU_NOTE_PUNCH_IN, MCU_NOTE_METRONOME.</done>
</task>

<task type="checkpoint:human-verify" gate="blocking">
  <name>Task 2: Hardware verification — pickup mode and mode LED note numbers</name>
  <files>src/mcuConfig.h</files>
  <action>Upload firmware and verify pickup mode FSM and LED-03 mode button note numbers against Logic Pro. Update src/mcuConfig.h if observed note numbers differ from community-sourced values (MCU_NOTE_LOOP=86, MCU_NOTE_PUNCH_IN=85, MCU_NOTE_METRONOME=89).</action>
  <verify>
    <automated>cd /Users/kenmarut/repo/phaedr-midi-controller && pio run --target upload 2>&1 | tail -5</automated>
    <manual>Human verifies pickup blink behavior and mode LED note numbers against Logic Pro — see how-to-verify section below.</manual>
  </verify>
  <done>Pickup mode and mode LEDs verified working on hardware. Note numbers confirmed or corrected in mcuConfig.h.</done>
  <what-built>
Phase 2 firmware integration is complete. Upload the firmware to the Teensy and test against Logic Pro:

- Pickup mode FSM: After a bank switch in Logic, physically move a fader. The channel strip button (P1–P8) should begin blinking. Sweep the fader to where Logic's on-screen fader is positioned — the blink should stop and the fader should resume sending pitch bend.
- Mode LEDs: Toggle Loop (cycle), Punch In, and Metronome in Logic. Watch the grid button LEDs K9, K10, K11 respectively.
- Blink rate: The blink should be faster when the fader is far from the DAW target and slow as it approaches.
  </what-built>
  <how-to-verify>
1. Build and upload: `pio run --target upload`

2. **Pickup mode test (PICK-01 through PICK-06):**
   a. In Logic, switch banks (Bank Prev/Next on the controller — or click a different bank in Logic's mixer)
   b. Move a physical fader slowly. The corresponding channel strip button (P1–P8) should start blinking.
   c. Move the fader to where Logic's on-screen fader shows. Blink should stop. A MIDI monitor should show one pitch bend message sent at that moment (snap value).
   d. Move the fader away from center — blink restarts faster. Move it back toward target — blink slows.
   e. Set Logic fader and physical fader both to 0 (full down). Fader should pick up immediately (boundary edge case PICK-06).

3. **LED-03 mode button test — note number verification:**
   a. Open Logic's MIDI Monitor (Window > MIDI > Incoming) or use a MIDI monitor app.
   b. In Logic, click the Cycle button ON and OFF. Note the Note numbers in the MIDI monitor.
   c. Click Punch In/Out ON and OFF. Note the Note numbers.
   d. Click Metronome ON and OFF. Note the Note numbers.
   e. Compare the observed note numbers against the values in `src/mcuConfig.h`:
      - MCU_NOTE_LOOP (currently: 86)
      - MCU_NOTE_PUNCH_IN (currently: 85)
      - MCU_NOTE_METRONOME (currently: 89)
   f. Watch K9/K10/K11 (the 3rd row of the grid, leftmost 3 buttons) for LED state changes when you toggle each mode in Logic.

4. **Note number correction (if needed):** If the observed note numbers differ from mcuConfig.h values, report the correct values. The notes will be updated in mcuConfig.h before marking this checkpoint complete.
  </how-to-verify>
  <resume-signal>
Type "approved" if pickup mode and mode LEDs work correctly.
If note numbers are wrong, report the correct values observed in the MIDI monitor (e.g., "Loop is note 71, Punch is 69, Metro is 59") and those will be updated in mcuConfig.h.
  </resume-signal>
</task>

</tasks>

<verification>
1. `pio run` exits 0 — firmware builds cleanly with all 4 files modified
2. Hardware test: fader pickup mode blinks channel button after bank switch and on first fader move
3. Hardware test: blink stops at crossover point; pitch bend snap value sent immediately
4. Hardware test: mode LEDs (Loop/Punch/Metro) respond to Logic's state toggles on K9/K10/K11
5. Human checkpoint approved — note numbers confirmed correct or updated in mcuConfig.h
</verification>

<success_criteria>
Phase 2 complete when:
1. Build: `pio run` exits 0 with all Phase 2 files in place
2. PICK-01: Logic fader DAW values flow into firmware via pitch bend receive callback
3. PICK-02: Fader MIDI output suppressed after bank switch until physical crosses DAW target
4. PICK-03: Channel button blinks (variable rate) after first fader move post-bank-switch
5. PICK-04: Blink stops exactly at crossover; snap pitch bend sent to DAW
6. PICK-05: Each fader independently detects its own bank switch via delta threshold
7. PICK-06: Boundary edge (both at 0 or both at 127) triggers immediate pickup
8. LED-03: Loop/Punch/Metronome grid button LEDs reflect Logic Pro's cycle/punch/metro state
9. Human checkpoint: confirmed working on hardware, note numbers verified or corrected
</success_criteria>

<output>
After completion, create `.planning/phases/02-led-state-pickup-mode/02-03-SUMMARY.md`
</output>
